gfaout/Gamma-Smartwatch/Firmware/Gamma/Gamma.ino

//#include "GammaPower.h"
#include "GammaPPG.h"

GammaPPG ppg;

void setup() {
  // put your setup code here, to run once:
  Serial.begin(9600);
  ppg.begin();

}

void loop() {
  // put your main code here, to run repeatedly:

}
