gfaout/Gamma-Smartwatch/Firmware/Gamma/GammaSettings.cpp

#include "GammaSettings.h"

const char* settingsFile = "settings.json"

GammaSettings::GammaSettings() 
{
  
}
void GammaSettings::begin()
{
}

void GammaSettings::loadFromFile(char* filename)
{

}

void GammaSettings::saveToFile(char* filename)
{

}
